KataFF/tbt-pcie-adapter/connectors.kicad_sch

## KiCad design connectors.kicad_sch (2025-07-04)

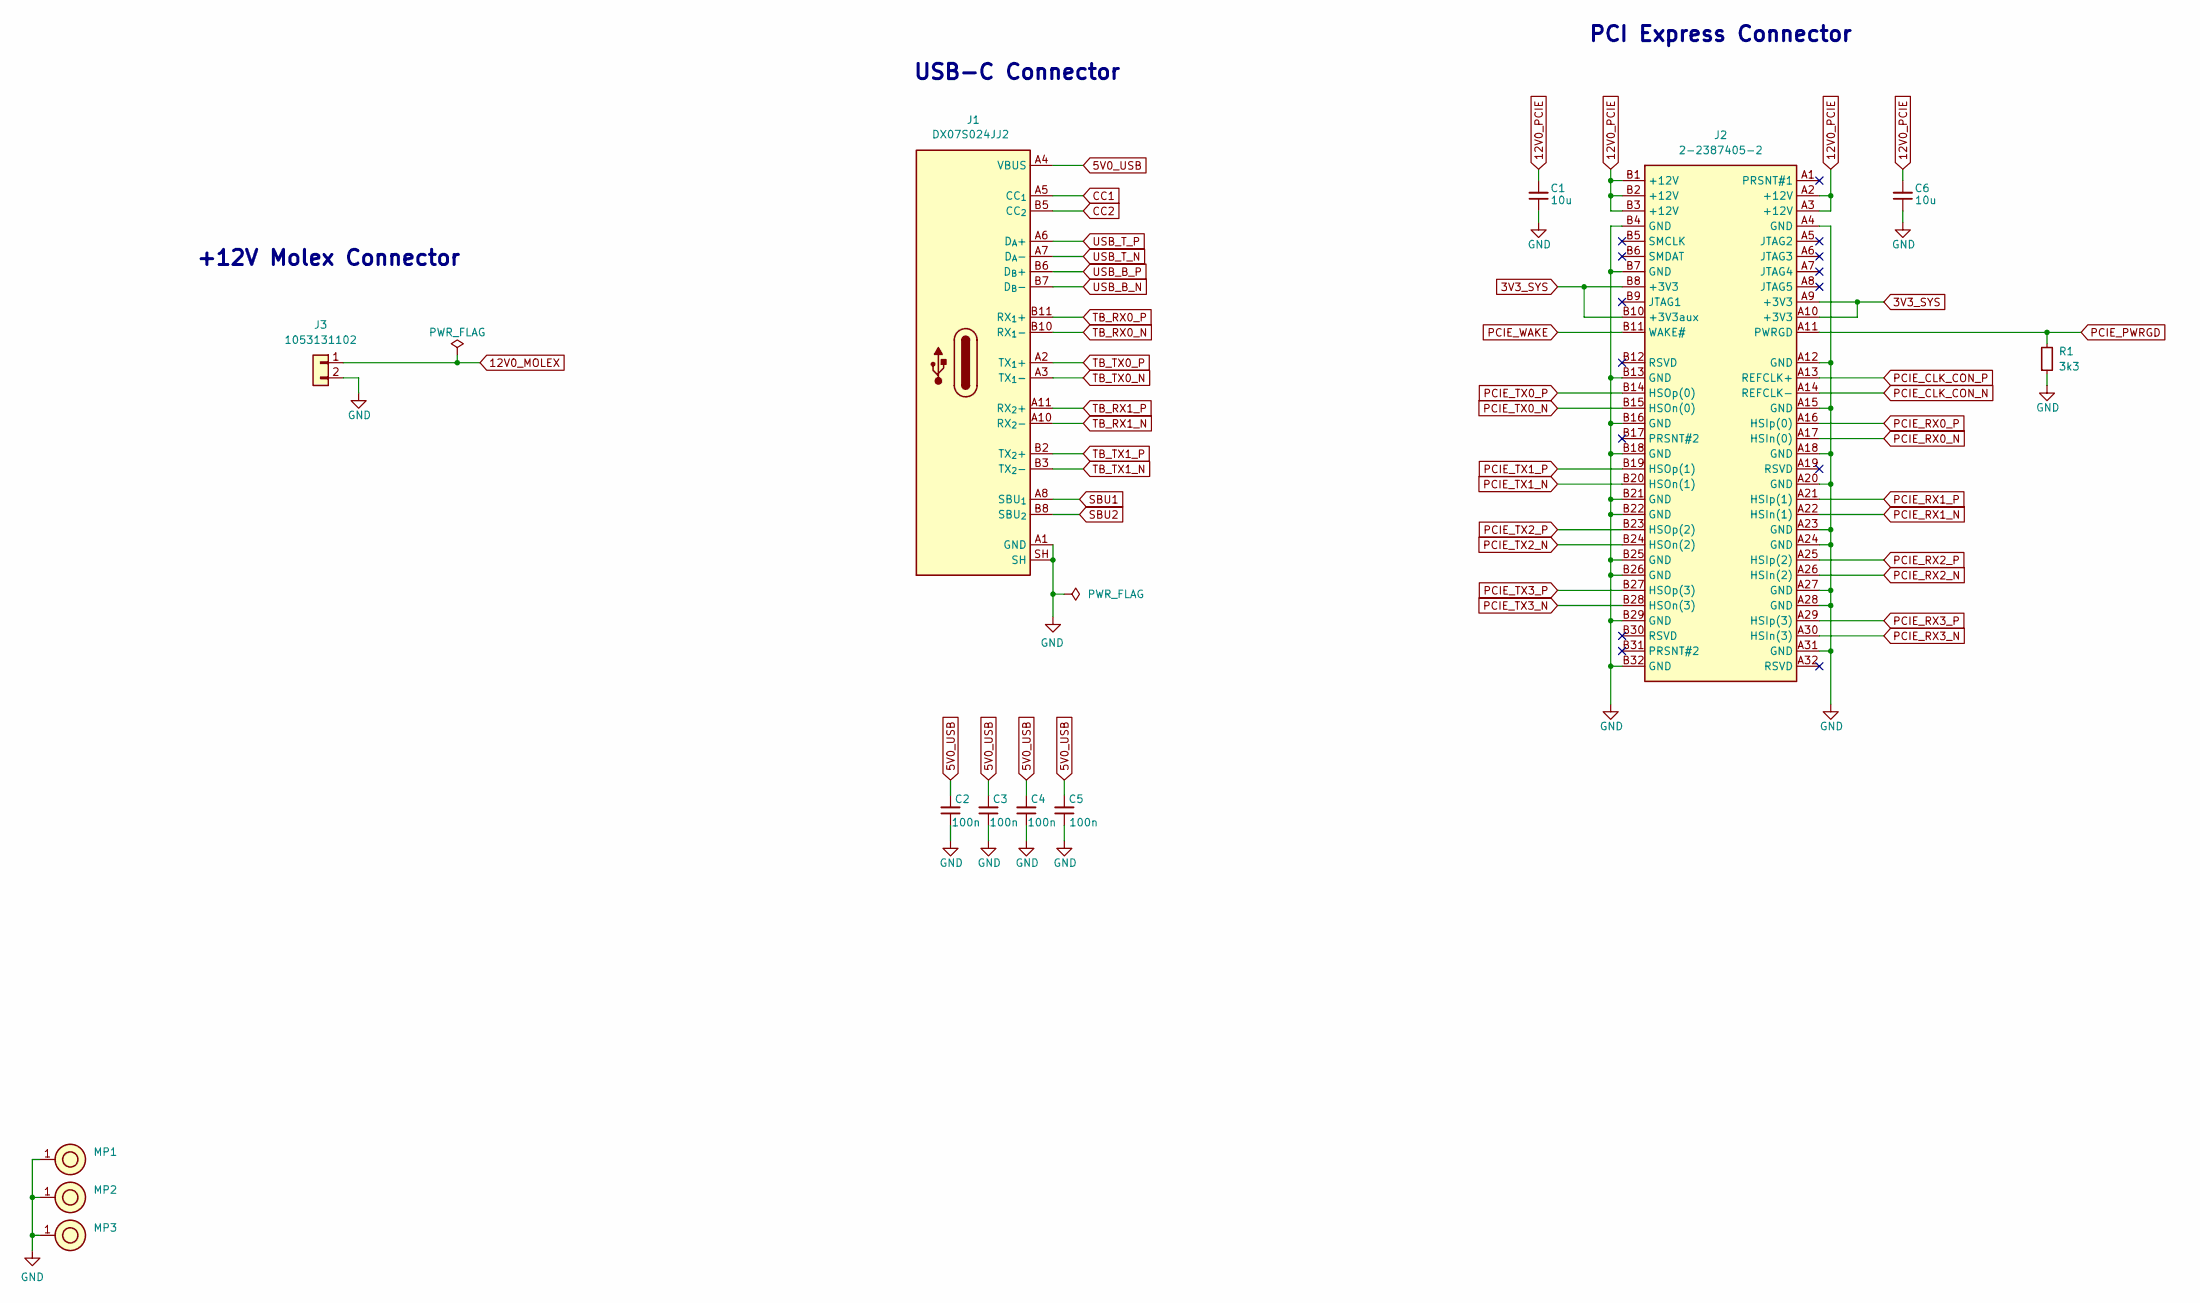
[picture p2: schematic connectors.kicad_sch]

Parts:
C1, C6: C_10u_0805_35V; C_0805_2012Metric; Voltage 35V; MPN GRM21BR6YA106KE43L
C2, C3, C4, C5: C_100n_0402; C_0402_1005Metric; Voltage 50V; MPN GRM155R61H104KE14D
J1: USB-C_JAE_DX07S024JJ2; USB-C_Receptacle_JAE_DX07S024JJ2; MPN DX07S024JJ2
J2: PCIe_x4_Conn_EdgeMount_Open; PCIE_TE_2-2387405-2; MPN 2-2387405-2
J3: Molex_Nano-Fit_1x2_1053131102; Conn_Molex_Nano-Fit_1x2_1053131102; MPN 1053131102
MP1, MP2, MP3: MP_Pad6mm_Drill3mm
R1: R_3k3_0402; R_0402_1005Metric; Tolerance 1%; MPN CR0402-FX-3301GLF

Connections:
3V3_SYS: J2.A9 (+3V3), J2.A10 (+3V3), J2.B8 (+3V3), J2.B10 (+3V3aux)
5V0_USB: C2.2, C3.2, C4.2, C5.2, J1.A4 (VBUS), J1.A9 (VBUS), J1.B4 (VBUS), J1.B9 (VBUS)
12V0_MOLEX: J3.1
12V0_PCIE: C1.2, C6.2, J2.A2 (+12V), J2.A3 (+12V), J2.B1 (+12V), J2.B2 (+12V), J2.B3 (+12V)
CC1: J1.A5 (CC_{1})
CC2: J1.B5 (CC_{2})
GND: C1.1, C2.1, C3.1, C4.1, C5.1, C6.1, J1.A1 (GND), J1.A12 (GND), J1.B1 (GND), J1.B12 (GND), J1.SH, J2.A4 (GND), J2.A12 (GND), J2.A15 (GND), J2.A18 (GND), J2.A20 (GND), J2.A23 (GND), J2.A24 (GND), J2.A27 (GND), J2.A28 (GND), J2.A31 (GND), J2.B4 (GND), J2.B7 (GND), J2.B13 (GND), J2.B16 (GND), J2.B18 (GND), J2.B21 (GND), J2.B22 (GND), J2.B25 (GND), J2.B26 (GND), J2.B29 (GND), J2.B32 (GND), J3.2, MP1.1, MP2.1, MP3.1, R1.1
PCIE_CLK_CON_N: J2.A14 (REFCLK-)
PCIE_CLK_CON_P: J2.A13 (REFCLK+)
PCIE_PWRGD: J2.A11 (PWRGD), R1.2
PCIE_RX0_N: J2.A17 (HSIn(0))
PCIE_RX0_P: J2.A16 (HSIp(0))
PCIE_RX1_N: J2.A22 (HSIn(1))
PCIE_RX1_P: J2.A21 (HSIp(1))
PCIE_RX2_N: J2.A26 (HSIn(2))
PCIE_RX2_P: J2.A25 (HSIp(2))
PCIE_RX3_N: J2.A30 (HSIn(3))
PCIE_RX3_P: J2.A29 (HSIp(3))
PCIE_TX0_N: J2.B15 (HSOn(0))
PCIE_TX0_P: J2.B14 (HSOp(0))
PCIE_TX1_N: J2.B20 (HSOn(1))
PCIE_TX1_P: J2.B19 (HSOp(1))
PCIE_TX2_N: J2.B24 (HSOn(2))
PCIE_TX2_P: J2.B23 (HSOp(2))
PCIE_TX3_N: J2.B28 (HSOn(3))
PCIE_TX3_P: J2.B27 (HSOp(3))
PCIE_WAKE: J2.B11 (WAKE#)
SBU1: J1.A8 (SBU_{1})
SBU2: J1.B8 (SBU_{2})
TB_RX0_N: J1.B10 (RX_{1}-)
TB_RX0_P: J1.B11 (RX_{1}+)
TB_RX1_N: J1.A10 (RX_{2}-)
TB_RX1_P: J1.A11 (RX_{2}+)
TB_TX0_N: J1.A3 (TX_{1}-)
TB_TX0_P: J1.A2 (TX_{1}+)
TB_TX1_N: J1.B3 (TX_{2}-)
TB_TX1_P: J1.B2 (TX_{2}+)
USB_B_N: J1.B7 (D_{B}-)
USB_B_P: J1.B6 (D_{B}+)
USB_T_N: J1.A7 (D_{A}-)
USB_T_P: J1.A6 (D_{A}+)

Notes on the sheet:
+12V Molex Connector
PCI Express Connector
USB-C Connector
