KataFF/tbt-pcie-adapter/power.kicad_sch

## KiCad design power.kicad_sch (2025-07-04)

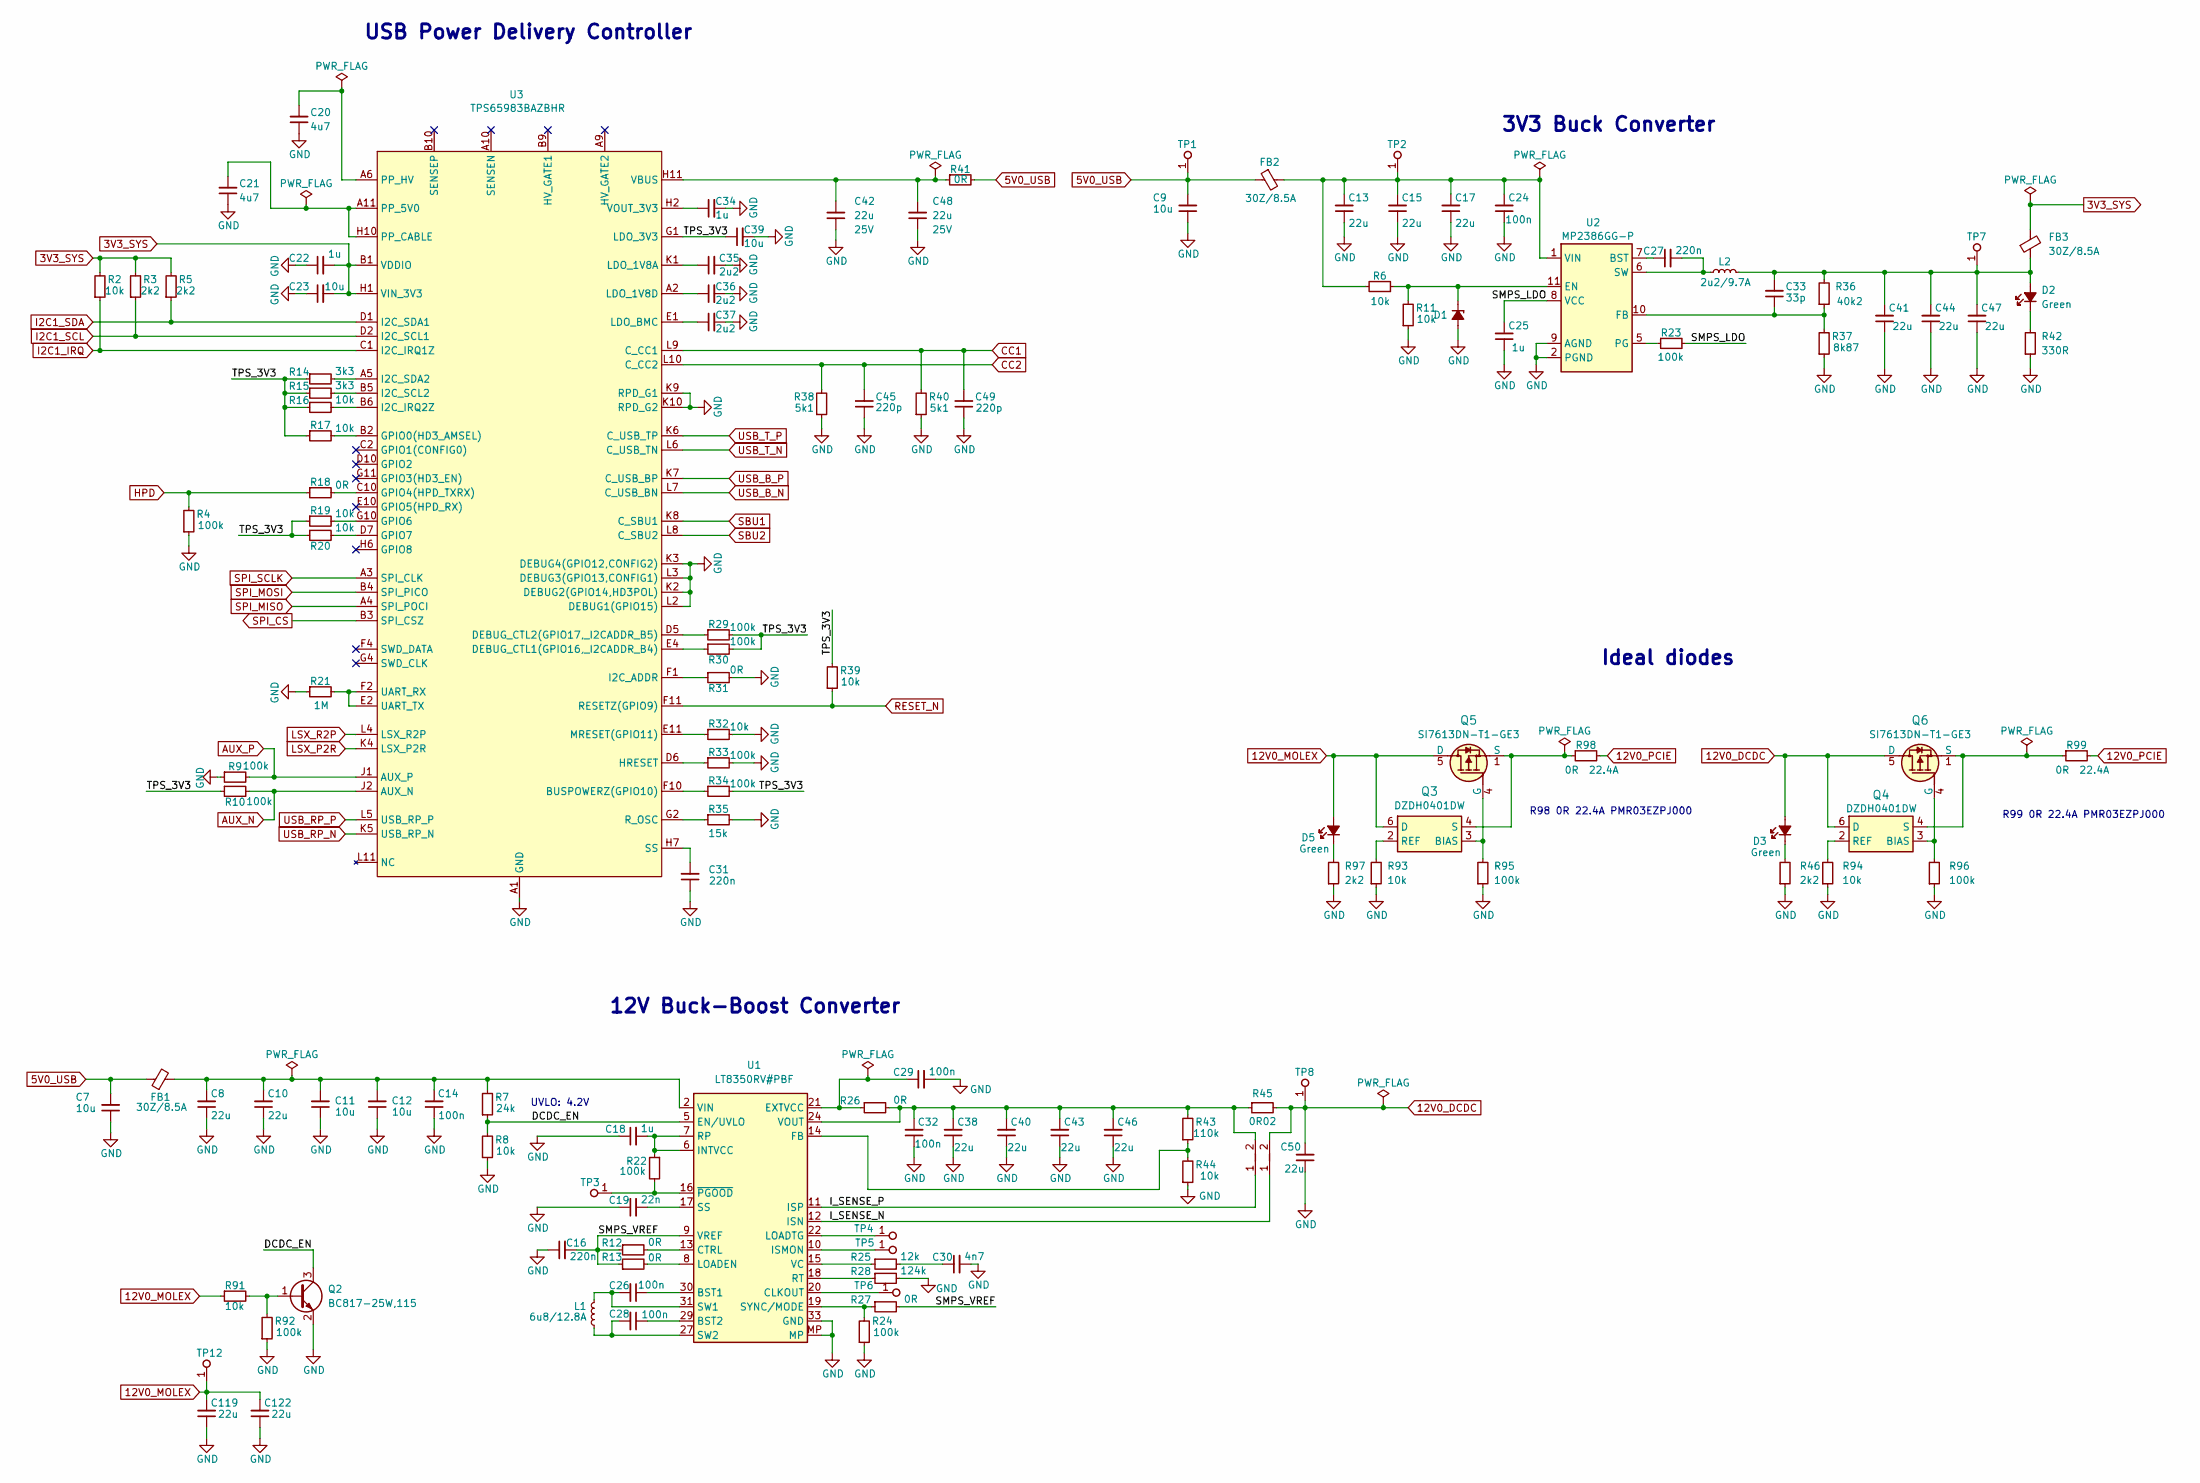
[picture p3: schematic power.kicad_sch]

Parts:
C7, C9, C11, C12: C_10u_0805_35V; C_0805_2012Metric; Voltage 35V; MPN GRM21BR6YA106KE43L
C8, C10, C13, C15, C17: C_22u_1206_35V; C_1206_3216Metric; Voltage 35V; MPN 3216X5R1V226M160AC
C14, C24, C26, C28, C29, C32: C_100n_0402; C_0402_1005Metric; Voltage 50V; MPN GRM155R61H104KE14D
C16, C27, C31: C_220n_0402; C_0402_1005Metric; MPN CC0402KRX5R6BB224
C18, C22, C25, C34: C_1u_0402; C_0402_1005Metric; MPN C1005X6S1A105K050BC
C19: C_22n_0402; C_0402_1005Metric; MPN GCM155R71H223MA55D
C20, C21: C_4u7_25V_0402; C_0402_1005Metric; Voltage 25V; MPN GRM155C61E475ME15J
C23, C39: C_10u_0402; C_0402_1005Metric; MPN CC0402MRX5R5BB106
C30: C_4n7_0402; C_0402_1005Metric; MPN CGA2B3X7S2A472K050BB
C33: C_33p_0402; C_0402_1005Metric; MPN 04025A330FAT2A
C35, C36, C37: C_2u2_0402; C_0402_1005Metric; MPN C1005X5R1A225K050BC
C38, C40, C43, C46, C50, C119, C122: C_22u_16V_0603; C_0603_1608Metric; Voltage 16V; MPN CL10A226MO7JZNC
C41, C44, C47: C_22u_0603; C_0603_1608Metric; MPN GRM188R60J226MEA0D
C42, C48: C_22u_25V_0805; C_0805_2012Metric; Voltage 25V; MPN CL21A226MAYNNNE
C45, C49: C_220p_0402; C_0402_1005Metric; MPN 04025C221JAT2A
D1: MM3Z3V3C; D_SOD-323F; MPN MM3Z3V3C
D2, D3, D5: LED_G_0603_KP-1608CGCK; LED_0603_1608Metric_G; MPN KP-1608CGCK
FB1, FB2, FB3: FB_30Z_8.5A_Murata-BLM21SN_0805; FB_0805_2012Metric; MPN BLM21SN300SZ1D
L1: L_6u8_12.8A_Coilcraft-XAL7070; L_Coilcraft-XAL7070; MPN XAL7070-682MEC
L2: L_2u2_9.7A_Coilcraft-XAL5030; L_Coilcraft-XAL5030; MPN XAL5030-222MEC
Q2: BC817-25W; SOT-323; MPN BC817-25W,115
Q3, Q4: DZDH0401DW; SOT-363; MPN DZDH0401DW
Q5, Q6: SI7613DN-T1-GE3; Vishay_PowerPAK_1212-8_Single; MPN SI7613DN-T1-GE3
R2, R6, R8, R11, R16, R17, R19, R20, R32, R39, R44, R91, R93, R94: R_10k_0402; R_0402_1005Metric; Tolerance 1%; MPN CR0402-FX-1002GLF
R3, R5, R46, R97: R_2k2_0402; R_0402_1005Metric; Tolerance 1%; MPN CR0402-FX-2201GLF
R4, R9, R10, R22, R23, R24, R29, R30, R33, R34, R92, R95, R96: R_100k_0402; R_0402_1005Metric; Tolerance 1%; MPN CR0402-FX-1003GLF
R7: R_24k_0402; R_0402_1005Metric; Tolerance 1%; MPN CR0402-FX-2402GLF
R12, R13, R18, R26, R27, R31: R_0R_0402; R_0402_1005Metric; MPN ERJ2GE0R00X
R14, R15: R_3k3_0402; R_0402_1005Metric; Tolerance 1%; MPN CR0402-FX-3301GLF
R21: R_1M_0402; R_0402_1005Metric; Tolerance 1%; MPN CR0402-FX-1004GLF
R25: R_12k_0402; R_0402_1005Metric; Tolerance 1%; MPN CR0402-FX-1202GLF
R28: R_124k_0402; R_0402_1005Metric; Tolerance 1%; MPN CR0402-FX-1243GLF
R35: R_15k_0.1%_0402; R_0402_1005Metric; Tolerance 0.1%; MPN ERA-2ARB153X
R36: R_40k2_0402; R_0402_1005Metric; Tolerance 1%; MPN CR0402-FX-4022GLF
R37: R_8k87_0402; R_0402_1005Metric; Tolerance 1%; MPN CR0402-FX-8871GLF
R38, R40: R_5k1_0402; R_0402_1005Metric; Tolerance 1%; MPN CR0402-FX-5101GLF
R41: R_0R_0603; R_0603_1608Metric; MPN CR0603-J/-000ELF
R42: R_330R_0402; R_0402_1005Metric; Tolerance 1%; MPN CR0402-FX-3300GLF
R43: R_110k_0402; R_0402_1005Metric; Tolerance 1%; MPN CR0402-FX-1103GLF
R45: R_0R02_1206; R_1206_3216Metric; Tolerance 1%; MPN WSLP1206R0200FEA
R98, R99: R_0R_22.4A_0603; R_0603_1608Metric; Tolerance template_tolerance; MPN PMR03EZPJ000
TP1, TP2, TP3, TP5, TP7, TP8, TP12: TP_1mm_SMD; TP_SMD_1mm
TP4, TP6: TP_0.75mm_SMD; TP_SMD_0.75mm
TP10, TP11: Net-Tie_P0.1mm; NetTie-2_SMD_Pad0.1mm
U1: LT8350RV; QFN-32-4EP_4x6mm_P0.5mm; MPN LT8350RV#PBF
U2: MP2386GG; QFN-11_2x2mm_P0.5mm; MPN MP2386GG-P
U3: TPS65983BAZBHR; IC_TPS65983BAZBHR; MPN TPS65983BAZBHR

Connections:
3V3_SYS: C22.2, C23.2, FB3.2, R2.2, R3.2, R5.2, U3.B1 (VDDIO), U3.H1 (VIN_3V3)
5V0_USB: C7.2, C9.2, FB1.1, FB2.1, R41.2, TP1.1
12V0_DCDC: C50.2, D3.2 (A), Q4.6 (D), Q6.5 (D), R45.2, TP8.1, TP11.2
12V0_MOLEX: C119.2, C122.2, D5.2 (A), Q3.6 (D), Q5.5 (D), R91.1, TP12.1
12V0_PCIE: R98.2, R99.2
AUX_N: R10.2, U3.J2 (AUX_N)
AUX_P: R9.2, U3.J1 (AUX_P)
CC1: C49.2, R40.2, U3.L9 (C_CC1)
CC2: C45.2, R38.2, U3.L10 (C_CC2)
DCDC_EN: Q2.3 (C), R7.1, R8.2, U1.5 (EN/UVLO)
GND: C7.1, C8.1, C9.1, C10.1, C11.1, C12.1, C13.1, C14.1, C15.1, C16.1, C17.1, C18.1, C19.1, C20.1, C21.1, C22.1, C23.1, C24.1, C25.1, C29.2, C30.2, C31.1, C32.1, C34.2, C35.2, C36.2, C37.2, C38.1, C39.2, C40.1, C41.1, C42.1, C43.1, C44.1, C45.1, C46.1, C47.1, C48.1, C49.1, C50.1, C119.1, C122.1, D1.2 (A), Q2.2 (E), R4.1, R8.1, R9.1, R11.1, R21.1, R24.1, R28.2, R31.2, R32.2, R33.2, R35.2, R37.1, R38.1, R40.1, R42.1, R44.1, R46.1, R92.1, R93.1, R94.1, R95.1, R96.1, R97.1, U1.33 (GND), U1.34 (GND), U1.35 (GND), U1.36 (GND), U1.MP, U2.2 (PGND), U2.3 (PGND), U2.4 (PGND), U2.9 (AGND), U3.A1 (GND), U3.B8 (GND), U3.D8 (GND), U3.E5 (GND), U3.E6 (GND), U3.E7 (GND), U3.E8 (GND), U3.F5 (GND), U3.F6 (GND), U3.F7 (GND), U3.F8 (GND), U3.G5 (GND), U3.G6 (GND), U3.G7 (GND), U3.G8 (GND), U3.H4 (GND), U3.H5 (GND), U3.H8 (GND), U3.K2 (DEBUG2(GPIO14,HD3POL)), U3.K3 (DEBUG4(GPIO12,CONFIG2)), U3.K9 (RPD_G1), U3.K10 (RPD_G2), U3.L1 (GND), U3.L2 (DEBUG1(GPIO15)), U3.L3 (DEBUG3(GPIO13,CONFIG1))
HPD: R4.2, R18.1
I2C1_IRQ: R2.1, U3.C1 (I2C_IRQ1Z)
I2C1_SCL: R3.1, U3.D2 (I2C_SCL1)
I2C1_SDA: R5.1, U3.D1 (I2C_SDA1)
I_SENSE_N: TP11.1, U1.12 (ISN)
I_SENSE_P: TP10.1, U1.11 (ISP)
LSX_P2R: U3.K4 (LSX_P2R)
LSX_R2P: U3.L4 (LSX_R2P)
unnamed: C8.2, C10.2, C11.2, C12.2, C14.2, FB1.2, R7.2, U1.2 (VIN), U1.3 (VIN)
unnamed: C13.2, C15.2, C17.2, C24.2, FB2.2, R6.2, TP2.1, U2.1 (VIN)
unnamed: C18.2, R22.1, U1.6 (INTVCC), U1.7 (RP)
unnamed: C19.2, U1.17 (SS)
unnamed: C20.2, U3.A6 (PP_HV), U3.A7 (PP_HV), U3.A8 (PP_HV), U3.B7 (PP_HV)
unnamed: C21.2, U3.A11 (PP_5V0), U3.B11 (PP_5V0), U3.C11 (PP_5V0), U3.D11 (PP_5V0), U3.H10 (PP_CABLE)
unnamed: C26.1, U1.30 (BST1)
unnamed: C26.2, L1.1, U1.31 (SW1), U1.32 (SW1)
unnamed: C27.1, U2.7 (BST)
unnamed: C27.2, L2.1, U2.6 (SW)
unnamed: C28.1, U1.29 (BST2)
unnamed: C28.2, L1.2, U1.27 (SW2), U1.28 (SW2)
unnamed: C29.1, R26.1, U1.21 (EXTVCC)
unnamed: C30.1, R25.2
unnamed: C31.2, U3.H7 (SS)
unnamed: C32.2, C38.2, C40.2, C43.2, C46.2, R26.2, R43.2, R45.1, TP10.2, U1.24 (VOUT), U1.25 (VOUT)
unnamed: C33.1, R36.1, R37.2, U2.10 (FB)
unnamed: C33.2, C41.2, C44.2, C47.2, D2.2 (A), FB3.1, L2.2, R36.2, TP7.1
unnamed: C34.1, U3.H2 (VOUT_3V3)
unnamed: C35.1, U3.K1 (LDO_1V8A)
unnamed: C36.1, U3.A2 (LDO_1V8D)
unnamed: C37.1, U3.E1 (LDO_BMC)
unnamed: C42.2, C48.2, R41.1, U3.H11 (VBUS), U3.J10 (VBUS), U3.J11 (VBUS), U3.K11 (VBUS)
unnamed: D1.1 (C), R6.1, R11.2, U2.11 (EN)
unnamed: D2.1 (C), R42.2
unnamed: D3.1 (C), R46.2
unnamed: D5.1 (C), R97.2
unnamed: Q2.1 (B), R91.2, R92.2
unnamed: Q3.2 (REF), R93.2
unnamed: Q3.3 (BIAS), Q5.4 (G), R95.2
unnamed: Q3.4 (S), Q5.1 (S), Q5.2 (S), Q5.3 (S), R98.1
unnamed: Q4.2 (REF), R94.2
unnamed: Q4.3 (BIAS), Q6.4 (G), R96.2
unnamed: Q4.4 (S), Q6.1 (S), Q6.2 (S), Q6.3 (S), R99.1
unnamed: R12.2, U1.13 (CTRL)
unnamed: R13.2, U1.8 (LOADEN)
unnamed: R14.2, U3.A5 (I2C_SDA2)
unnamed: R15.2, U3.B5 (I2C_SCL2)
unnamed: R16.2, U3.B6 (I2C_IRQ2Z)
unnamed: R17.2, U3.B2 (GPIO0(HD3_AMSEL))
unnamed: R18.2, U3.C10 (GPIO4(HPD_TXRX))
unnamed: R19.2, U3.G10 (GPIO6)
unnamed: R20.2, U3.D7 (GPIO7)
unnamed: R21.2, U3.E2 (UART_TX), U3.F2 (UART_RX)
unnamed: R22.2, TP3.1, U1.16 (~PGOOD)
unnamed: R23.1, U2.5 (PG)
unnamed: R24.2, R27.1, U1.19 (SYNC/MODE)
unnamed: R25.1, U1.15 (VC)
unnamed: R28.1, U1.18 (RT)
unnamed: R29.1, U3.D5 (DEBUG_CTL2(GPIO17,_I2CADDR_B5))
unnamed: R30.1, U3.E4 (DEBUG_CTL1(GPIO16,_I2CADDR_B4))
unnamed: R31.1, U3.F1 (I2C_ADDR)
unnamed: R32.1, U3.E11 (MRESET(GPIO11))
unnamed: R33.1, U3.D6 (HRESET)
unnamed: R34.1, U3.F10 (BUSPOWERZ(GPIO10))
unnamed: R35.1, U3.G2 (R_OSC)
unnamed: R43.1, R44.2, U1.14 (FB)
unnamed: TP4.1, U1.22 (LOADTG)
unnamed: TP5.1, U1.10 (ISMON)
unnamed: TP6.1, U1.20 (CLKOUT)
RESET_N: R39.1, U3.F11 (RESETZ(GPIO9))
SBU1: U3.K8 (C_SBU1)
SBU2: U3.L8 (C_SBU2)
SMPS_LDO: C25.2, R23.2, U2.8 (VCC)
SMPS_VREF: C16.2, R12.1, R13.1, R27.2, U1.9 (VREF)
SPI_CS: U3.B3 (SPI_CSZ)
SPI_MISO: U3.A4 (SPI_POCI)
SPI_MOSI: U3.B4 (SPI_PICO)
SPI_SCLK: U3.A3 (SPI_CLK)
TPS_3V3: C39.1, R10.1, R14.1, R15.1, R16.1, R17.1, R19.1, R20.1, R29.2, R30.2, R34.2, R39.2, U3.G1 (LDO_3V3)
USB_B_N: U3.L7 (C_USB_BN)
USB_B_P: U3.K7 (C_USB_BP)
USB_RP_N: U3.K5 (USB_RP_N)
USB_RP_P: U3.L5 (USB_RP_P)
USB_T_N: U3.L6 (C_USB_TN)
USB_T_P: U3.K6 (C_USB_TP)

Notes on the sheet:
UVLO: 4.2V
R99 0R 22.4A PMR03EZPJ000
Ideal diodes
USB Power Delivery Controller
12V Buck-Boost Converter
3V3 Buck Converter
R98 0R 22.4A PMR03EZPJ000
