KataFF/tbt-pcie-adapter/tb-power.kicad_sch

## KiCad design tb-power.kicad_sch (2025-07-04)

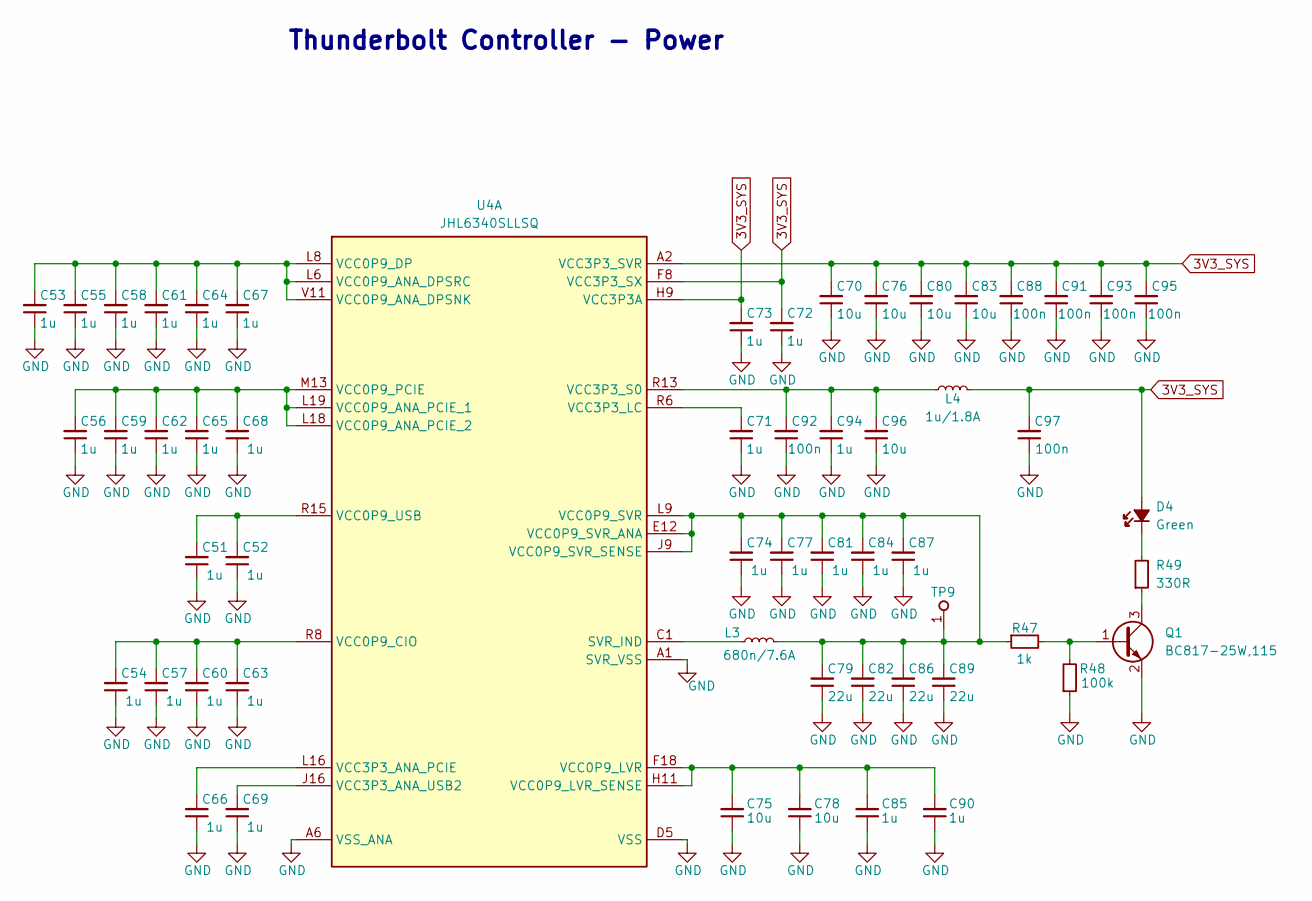
[picture p4: schematic tb-power.kicad_sch]

Parts:
C51, C52, C53, C54, C55, C56, C57, C58, C59, C60, C61, C62, C63, C64, C65, C66, C67, C68, C69, C71, C72, C73, C74, C77, C81, C84, C85, C87, C90, C94: C_1u_0402; C_0402_1005Metric; MPN C1005X6S1A105K050BC
C70, C75, C76, C78, C80, C83, C96: C_10u_0402; C_0402_1005Metric; MPN CC0402MRX5R5BB106
C79, C82, C86, C89: C_22u_0603; C_0603_1608Metric; MPN GRM188R60J226MEA0D
C88, C91, C92, C93, C95, C97: C_100n_0402; C_0402_1005Metric; Voltage 50V; MPN GRM155R61H104KE14D
D4: LED_G_0603_KP-1608CGCK; LED_0603_1608Metric_G; MPN KP-1608CGCK
L3: L_680n_7.6A_IHLP1616BZ; L_Vishay-IHLP1616BZ; MPN IHLP1616BZERR68M5A
L4: L_1u_1.8A_0603; L_0603_1608Metric; MPN DFE18SBN1R0ME0L
Q1: BC817-25W; SOT-323; MPN BC817-25W,115
R47: R_1k_0402; R_0402_1005Metric; Tolerance 1%; MPN CR0402-FX-1001GLF
R48: R_100k_0402; R_0402_1005Metric; Tolerance 1%; MPN CR0402-FX-1003GLF
R49: R_330R_0402; R_0402_1005Metric; Tolerance 1%; MPN CR0402-FX-3300GLF
TP9: TP_1mm_SMD; TP_SMD_1mm
U4: JHL6340SLLSQ; MPN JHL6340SLLSQ

Connections:
3V3_SYS: C70.2, C72.2, C73.2, C76.2, C80.2, C83.2, C88.2, C91.2, C93.2, C95.2, C97.2, D4.2 (A), L4.2, U4.A2 (VCC3P3_SVR), U4.A3 (VCC3P3_SVR), U4.B3 (VCC3P3_SVR), U4.F8 (VCC3P3_SX), U4.H9 (VCC3P3A)
GND: C51.1, C52.1, C53.1, C54.1, C55.1, C56.1, C57.1, C58.1, C59.1, C60.1, C61.1, C62.1, C63.1, C64.1, C65.1, C66.1, C67.1, C68.1, C69.1, C70.1, C71.1, C72.1, C73.1, C74.1, C75.1, C76.1, C77.1, C78.1, C79.1, C80.1, C81.1, C82.1, C83.1, C84.1, C85.1, C86.1, C87.1, C88.1, C89.1, C90.1, C91.1, C92.1, C93.1, C94.1, C95.1, C96.1, C97.1, Q1.2 (E), R48.1, U4.A1 (SVR_VSS), U4.A6 (VSS_ANA), U4.A8 (VSS_ANA), U4.A10 (VSS_ANA), U4.A12 (VSS_ANA), U4.A14 (VSS_ANA), U4.A16 (VSS_ANA), U4.A18 (VSS_ANA), U4.A20 (VSS_ANA), U4.A22 (VSS_ANA), U4.AA22 (VSS_ANA), U4.AA23 (VSS_ANA), U4.AB1 (VSS), U4.AB6 (VSS_ANA), U4.AB8 (VSS_ANA), U4.AB10 (VSS_ANA), U4.AB12 (VSS_ANA), U4.AB14 (VSS_ANA), U4.AB16 (VSS_ANA), U4.AB18 (VSS_ANA), U4.AB20 (VSS_ANA), U4.AB22 (VSS_ANA), U4.AC2 (VSS), U4.AC6 (VSS_ANA), U4.AC8 (VSS_ANA), U4.AC10 (VSS_ANA), U4.AC12 (VSS_ANA), U4.AC14 (VSS_ANA), U4.AC16 (VSS_ANA), U4.AC18 (VSS_ANA), U4.AC20 (VSS_ANA), U4.AC22 (VSS_ANA), U4.B1 (SVR_VSS), U4.B2 (SVR_VSS), U4.B6 (VSS_ANA), U4.B8 (VSS_ANA), U4.B10 (VSS_ANA), U4.B12 (VSS_ANA), U4.B14 (VSS_ANA), U4.B16 (VSS_ANA), U4.B18 (VSS_ANA), U4.B20 (VSS_ANA), U4.B22 (VSS_ANA), U4.D5 (VSS), U4.D8 (VSS_ANA), U4.D9 (VSS_ANA), U4.D11 (VSS_ANA), U4.D12 (VSS_ANA), U4.D13 (VSS_ANA), U4.D15 (VSS_ANA), U4.D16 (VSS_ANA), U4.D18 (VSS_ANA), U4.E4 (VSS), U4.E5 (VSS), U4.E6 (VSS), U4.E8 (VSS_ANA), U4.E9 (VSS_ANA), U4.E11 (VSS_ANA), U4.E15 (VSS_ANA), U4.E16 (VSS_ANA), U4.E22 (VSS_ANA), U4.E23 (VSS_ANA), U4.F5 (VSS), U4.F6 (VSS), U4.F9 (VSS_ANA), U4.F16 (VSS_ANA), U4.F20 (VSS_ANA), U4.G22 (VSS_ANA), U4.G23 (VSS_ANA), U4.H1 (VSS_ANA), U4.H2 (VSS_ANA), U4.H5 (VSS), U4.H8 (VSS), U4.H12 (VSS_ANA), U4.H13 (VSS_ANA), U4.H15 (VSS_ANA), U4.H16 (VSS_ANA), U4.H20 (VSS_ANA), U4.J5 (VSS_ANA), U4.J8 (VSS), U4.J12 (VSS), U4.J13 (VSS), U4.J15 (VSS), U4.J18 (VSS_ANA), U4.J19 (VSS_ANA), U4.J20 (VSS_ANA), U4.J22 (VSS_ANA), U4.J23 (VSS_ANA), U4.K1 (VSS_ANA), U4.K2 (VSS_ANA), U4.L5 (VSS_ANA), U4.L13 (VSS), U4.L20 (VSS_ANA), U4.L22 (VSS_ANA), U4.L23 (VSS_ANA), U4.M1 (VSS_ANA), U4.M2 (VSS_ANA), U4.M5 (VSS_ANA), U4.M11 (VSS), U4.M12 (VSS), U4.M19 (VSS_ANA), U4.M20 (VSS_ANA), U4.N5 (VSS_ANA), U4.N8 (VSS), U4.N9 (VSS), U4.N11 (VSS), U4.N12 (VSS), U4.N13 (VSS), U4.N20 (VSS_ANA), U4.N22 (VSS_ANA), U4.N23 (VSS_ANA), U4.P1 (VSS_ANA), U4.P2 (VSS_ANA), U4.R5 (VSS_ANA), U4.R18 (VSS_ANA), U4.R19 (VSS_ANA), U4.R20 (VSS_ANA), U4.R22 (VSS_ANA), U4.R23 (VSS_ANA), U4.T1 (VSS_ANA), U4.T2 (VSS_ANA), U4.T5 (VSS_ANA), U4.T6 (VSS), U4.T8 (VSS), U4.T9 (VSS), U4.T13 (VSS), U4.T15 (VSS), U4.T16 (VSS), U4.T18 (VSS), U4.T20 (VSS_ANA), U4.U22 (VSS_ANA), U4.U23 (VSS_ANA), U4.V5 (VSS_ANA), U4.V6 (VSS_ANA), U4.V8 (VSS_ANA), U4.V9 (VSS_ANA), U4.V15 (VSS_ANA), U4.V16 (VSS_ANA), U4.V20 (VSS_ANA), U4.W5 (VSS_ANA), U4.W6 (VSS_ANA), U4.W8 (VSS_ANA), U4.W9 (VSS_ANA), U4.W20 (VSS_ANA), U4.W22 (VSS_ANA), U4.W23 (VSS_ANA), U4.Y9 (VSS_ANA), U4.Y13 (VSS_ANA), U4.Y20 (VSS_ANA)
unnamed: C51.2, C52.2, U4.R15 (VCC0P9_USB), U4.R16 (VCC0P9_USB)
unnamed: C53.2, C55.2, C58.2, C61.2, C64.2, C67.2, U4.L6 (VCC0P9_ANA_DPSRC), U4.L8 (VCC0P9_DP), U4.L11 (VCC0P9_DP), U4.L12 (VCC0P9_DP), U4.M6 (VCC0P9_ANA_DPSRC), U4.M8 (VCC0P9_DP), U4.T11 (VCC0P9_DP), U4.T12 (VCC0P9_DP), U4.V11 (VCC0P9_ANA_DPSNK), U4.V12 (VCC0P9_ANA_DPSNK), U4.V13 (VCC0P9_ANA_DPSNK)
unnamed: C54.2, C57.2, C60.2, C63.2, U4.R8 (VCC0P9_CIO), U4.R9 (VCC0P9_CIO), U4.R11 (VCC0P9_CIO), U4.R12 (VCC0P9_CIO)
unnamed: C56.2, C59.2, C62.2, C65.2, C68.2, U4.L18 (VCC0P9_ANA_PCIE_2), U4.L19 (VCC0P9_ANA_PCIE_1), U4.M13 (VCC0P9_PCIE), U4.M15 (VCC0P9_PCIE), U4.M16 (VCC0P9_PCIE), U4.M18 (VCC0P9_ANA_PCIE_2), U4.N18 (VCC0P9_ANA_PCIE_2), U4.N19 (VCC0P9_ANA_PCIE_1)
unnamed: C66.2, U4.L16 (VCC3P3_ANA_PCIE)
unnamed: C69.2, U4.J16 (VCC3P3_ANA_USB2)
unnamed: C71.2, U4.R6 (VCC3P3_LC)
unnamed: C74.2, C77.2, C79.2, C81.2, C82.2, C84.2, C86.2, C87.2, C89.2, L3.2, R47.1, TP9.1, U4.E12 (VCC0P9_SVR_ANA), U4.E13 (VCC0P9_SVR_ANA), U4.F11 (VCC0P9_SVR_ANA), U4.F12 (VCC0P9_SVR_ANA), U4.F13 (VCC0P9_SVR_ANA), U4.F15 (VCC0P9_SVR_ANA), U4.J9 (VCC0P9_SVR_SENSE), U4.L9 (VCC0P9_SVR), U4.M9 (VCC0P9_SVR)
unnamed: C75.2, C78.2, C85.2, C90.2, U4.F18 (VCC0P9_LVR), U4.H11 (VCC0P9_LVR_SENSE), U4.H18 (VCC0P9_LVR), U4.J11 (VCC0P9_LVR)
unnamed: C92.2, C94.2, C96.2, L4.1, U4.R13 (VCC3P3_S0)
unnamed: D4.1 (C), R49.2
unnamed: L3.1, U4.C1 (SVR_IND), U4.C2 (SVR_IND), U4.D1 (SVR_IND)
unnamed: Q1.1 (B), R47.2, R48.2
unnamed: Q1.3 (C), R49.1

Notes on the sheet:
Thunderbolt Controller - Power
