KataFF/tbt-pcie-adapter/tb.kicad_sch

## KiCad design tb.kicad_sch (2025-07-04)

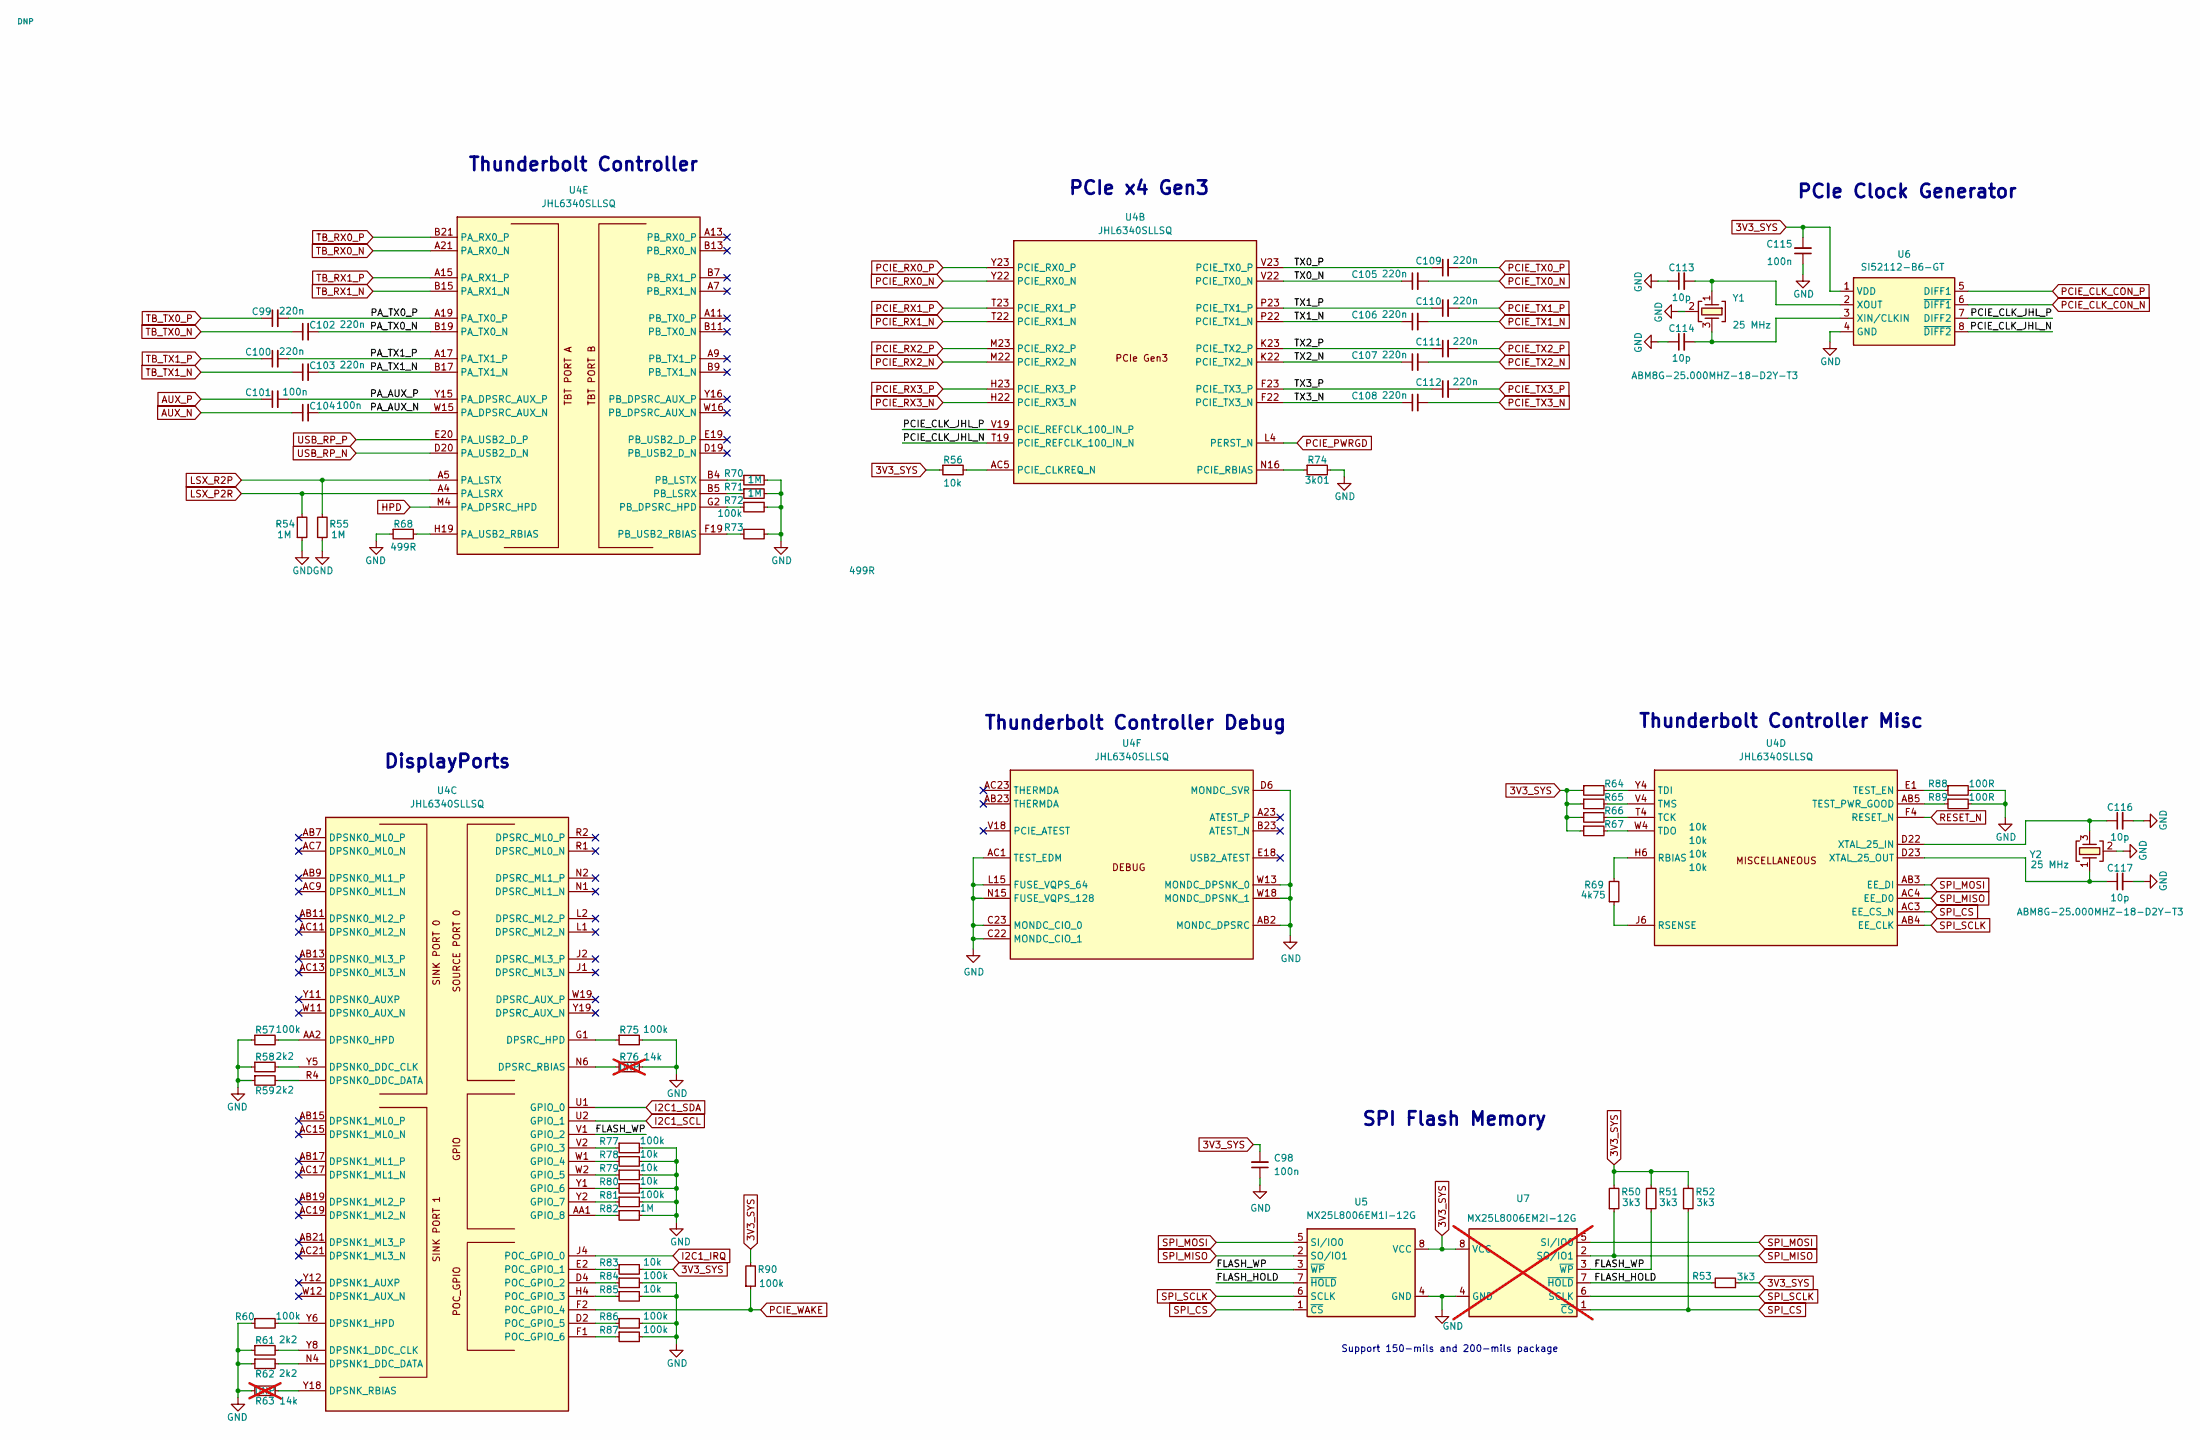
[picture p5: schematic tb.kicad_sch]

Parts:
C98, C101, C104, C115: C_100n_0402; C_0402_1005Metric; Voltage 50V; MPN GRM155R61H104KE14D
C99, C100, C102, C103, C105, C106, C107, C108, C109, C110, C111, C112: C_220n_0402; C_0402_1005Metric; MPN CC0402KRX5R6BB224
C113, C114, C116, C117: C_10p_0402; C_0402_1005Metric; Voltage 50V; MPN GCM1555C1H100GA16D
R50, R51, R52, R53: R_3k3_0402; R_0402_1005Metric; Tolerance 1%; MPN CR0402-FX-3301GLF
R54, R55, R70, R71, R82: R_1M_0402; R_0402_1005Metric; Tolerance 1%; MPN CR0402-FX-1004GLF
R56, R64, R65, R66, R67, R78, R79, R80, R83, R85: R_10k_0402; R_0402_1005Metric; Tolerance 1%; MPN CR0402-FX-1002GLF
R57, R60, R72, R75, R77, R81, R84, R86, R87, R90: R_100k_0402; R_0402_1005Metric; Tolerance 1%; MPN CR0402-FX-1003GLF
R58, R59, R61, R62: R_2k2_0402; R_0402_1005Metric; Tolerance 1%; MPN CR0402-FX-2201GLF
R63, R76: R_14k_0402; R_0402_1005Metric; Tolerance 1%; MPN CR0402-FX-1402GLF; not fitted
R68, R73: R_499R_0402; R_0402_1005Metric; Tolerance 1%; MPN CR0402-FX-4990GLF
R69: R_4k75_0.5%_0402; R_0402_1005Metric; Tolerance 0.5%; MPN ERJ-H2RD4751X
R74: R_3k01_0402; R_0402_1005Metric; Tolerance 1%; MPN CR0402-FX-3011GLF
R88, R89: R_100R_0402; R_0402_1005Metric; Tolerance 1%; MPN CR0402-FX-1000GLF
U4: JHL6340SLLSQ; MPN JHL6340SLLSQ
U5: MX25L8006EM1I-12G; SOIC-8_3.9x4.9x1.75mm_P1.27mm; MPN MX25L8006EM1I-12G
U6: SI52112-B6-GT; TSSOP-8_3x4.4mm_P0.65mm; MPN SI52112-B6-GT
U7: MX25L8006EM2I-12G; SOIC-8_5.3x5.3x2mm_P1.27mm; MPN MX25L8006EM2I-12G; not fitted
Y1, Y2: Resonator_25MHz_ABM8G; Resonator_SMD_Abracon_ABM8G_3.2x2.5mm; MPN ABM8G-25.000MHZ-18-D2Y-T3

Connections:
3V3_SYS: C98.2, C115.2, R50.2, R51.2, R52.2, R53.1, R56.1, R64.1, R65.1, R66.1, R67.1, R83.2, R90.2, U5.8 (VCC), U6.1 (VDD), U7.8 (VCC)
AUX_N: C104.1
AUX_P: C101.1
FLASH_HOLD: R53.2, U5.7 (~HOLD), U7.7 (~HOLD)
FLASH_WP: R51.1, U4.V1 (GPIO_2), U5.3 (~WP), U7.3 (~WP)
GND: C98.1, C113.1, C114.1, C115.1, C116.2, C117.2, R54.1, R55.1, R57.1, R58.1, R59.1, R60.1, R61.1, R62.1, R63.1, R68.1, R70.2, R71.2, R72.2, R73.2, R74.2, R75.2, R76.2, R77.2, R78.2, R79.2, R80.2, R81.2, R82.2, R84.2, R85.2, R86.2, R87.2, R88.2, R89.2, U4.AB2 (MONDC_DPSRC), U4.AC1 (TEST_EDM), U4.C22 (MONDC_CIO_1), U4.C23 (MONDC_CIO_0), U4.D6 (MONDC_SVR), U4.L15 (FUSE_VQPS_64), U4.N15 (FUSE_VQPS_128), U4.W13 (MONDC_DPSNK_0), U4.W18 (MONDC_DPSNK_1), U5.4 (GND), U6.4 (GND), U7.4 (GND), Y1.2 (SH), Y1.4 (SH), Y2.2 (SH), Y2.4 (SH)
HPD: U4.M4 (PA_DPSRC_HPD)
I2C1_IRQ: U4.J4 (POC_GPIO_0)
I2C1_SCL: U4.U2 (GPIO_1)
I2C1_SDA: U4.U1 (GPIO_0)
LSX_P2R: R54.2, U4.A4 (PA_LSRX)
LSX_R2P: R55.2, U4.A5 (PA_LSTX)
unnamed: C113.2, U6.2 (XOUT), Y1.1
unnamed: C114.2, U6.3 (XIN/CLKIN), Y1.3
unnamed: C116.1, U4.D22 (XTAL_25_IN), Y2.3
unnamed: C117.1, U4.D23 (XTAL_25_OUT), Y2.1
unnamed: R56.2, U4.AC5 (PCIE_CLKREQ_N)
unnamed: R57.2, U4.AA2 (DPSNK0_HPD)
unnamed: R58.2, U4.Y5 (DPSNK0_DDC_CLK)
unnamed: R59.2, U4.R4 (DPSNK0_DDC_DATA)
unnamed: R60.2, U4.Y6 (DPSNK1_HPD)
unnamed: R61.2, U4.Y8 (DPSNK1_DDC_CLK)
unnamed: R62.2, U4.N4 (DPSNK1_DDC_DATA)
unnamed: R63.2, U4.Y18 (DPSNK_RBIAS)
unnamed: R64.2, U4.Y4 (TDI)
unnamed: R65.2, U4.V4 (TMS)
unnamed: R66.2, U4.T4 (TCK)
unnamed: R67.2, U4.W4 (TDO)
unnamed: R68.2, U4.H19 (PA_USB2_RBIAS)
unnamed: R69.1, U4.J6 (RSENSE)
unnamed: R69.2, U4.H6 (RBIAS)
unnamed: R70.1, U4.B4 (PB_LSTX)
unnamed: R71.1, U4.B5 (PB_LSRX)
unnamed: R72.1, U4.G2 (PB_DPSRC_HPD)
unnamed: R73.1, U4.F19 (PB_USB2_RBIAS)
unnamed: R74.1, U4.N16 (PCIE_RBIAS)
unnamed: R75.1, U4.G1 (DPSRC_HPD)
unnamed: R76.1, U4.N6 (DPSRC_RBIAS)
unnamed: R77.1, U4.V2 (GPIO_3)
unnamed: R78.1, U4.W1 (GPIO_4)
unnamed: R79.1, U4.W2 (GPIO_5)
unnamed: R80.1, U4.Y1 (GPIO_6)
unnamed: R81.1, U4.Y2 (GPIO_7)
unnamed: R82.1, U4.AA1 (GPIO_8)
unnamed: R83.1, U4.E2 (POC_GPIO_1)
unnamed: R84.1, U4.D4 (POC_GPIO_2)
unnamed: R85.1, U4.H4 (POC_GPIO_3)
unnamed: R86.1, U4.D2 (POC_GPIO_5)
unnamed: R87.1, U4.F1 (POC_GPIO_6)
unnamed: R88.1, U4.E1 (TEST_EN)
unnamed: R89.1, U4.AB5 (TEST_PWR_GOOD)
PA_AUX_N: C104.2, U4.W15 (PA_DPSRC_AUX_N)
PA_AUX_P: C101.2, U4.Y15 (PA_DPSRC_AUX_P)
PA_TX0_N: C102.2, U4.B19 (PA_TX0_N)
PA_TX0_P: C99.2, U4.A19 (PA_TX0_P)
PA_TX1_N: C103.2, U4.B17 (PA_TX1_N)
PA_TX1_P: C100.2, U4.A17 (PA_TX1_P)
PCIE_CLK_CON_N: U6.6 (~DIFF1)
PCIE_CLK_CON_P: U6.5 (DIFF1)
PCIE_CLK_JHL_N: U4.T19 (PCIE_REFCLK_100_IN_N), U6.8 (~DIFF2)
PCIE_CLK_JHL_P: U4.V19 (PCIE_REFCLK_100_IN_P), U6.7 (DIFF2)
PCIE_PWRGD: U4.L4 (PERST_N)
PCIE_RX0_N: U4.Y22 (PCIE_RX0_N)
PCIE_RX0_P: U4.Y23 (PCIE_RX0_P)
PCIE_RX1_N: U4.T22 (PCIE_RX1_N)
PCIE_RX1_P: U4.T23 (PCIE_RX1_P)
PCIE_RX2_N: U4.M22 (PCIE_RX2_N)
PCIE_RX2_P: U4.M23 (PCIE_RX2_P)
PCIE_RX3_N: U4.H22 (PCIE_RX3_N)
PCIE_RX3_P: U4.H23 (PCIE_RX3_P)
PCIE_TX0_N: C105.2
PCIE_TX0_P: C109.2
PCIE_TX1_N: C106.2
PCIE_TX1_P: C110.2
PCIE_TX2_N: C107.2
PCIE_TX2_P: C111.2
PCIE_TX3_N: C108.2
PCIE_TX3_P: C112.2
PCIE_WAKE: R90.1, U4.F2 (POC_GPIO_4)
RESET_N: U4.F4 (RESET_N)
SPI_CS: R52.1, U4.AC3 (EE_CS_N), U5.1 (~CS), U7.1 (~CS)
SPI_MISO: R50.1, U4.AC4 (EE_D0), U5.2 (SO/IO1), U7.2 (SO/IO1)
SPI_MOSI: U4.AB3 (EE_DI), U5.5 (SI/IO0), U7.5 (SI/IO0)
SPI_SCLK: U4.AB4 (EE_CLK), U5.6 (SCLK), U7.6 (SCLK)
TB_RX0_N: U4.A21 (PA_RX0_N)
TB_RX0_P: U4.B21 (PA_RX0_P)
TB_RX1_N: U4.B15 (PA_RX1_N)
TB_RX1_P: U4.A15 (PA_RX1_P)
TB_TX0_N: C102.1
TB_TX0_P: C99.1
TB_TX1_N: C103.1
TB_TX1_P: C100.1
TX0_N: C105.1, U4.V22 (PCIE_TX0_N)
TX0_P: C109.1, U4.V23 (PCIE_TX0_P)
TX1_N: C106.1, U4.P22 (PCIE_TX1_N)
TX1_P: C110.1, U4.P23 (PCIE_TX1_P)
TX2_N: C107.1, U4.K22 (PCIE_TX2_N)
TX2_P: C111.1, U4.K23 (PCIE_TX2_P)
TX3_N: C108.1, U4.F22 (PCIE_TX3_N)
TX3_P: C112.1, U4.F23 (PCIE_TX3_P)
USB_RP_N: U4.D20 (PA_USB2_D_N)
USB_RP_P: U4.E20 (PA_USB2_D_P)

Notes on the sheet:
DisplayPorts
Thunderbolt Controller Misc
PCIe Clock Generator
SPI Flash Memory
Thunderbolt Controller
Thunderbolt Controller Debug
Support 150-mils and 200-mils package
PCIe x4 Gen3
