KataFF/tbt-pcie-adapter/thunderbolt-pcie-adapter.kicad_sch

## KiCad design thunderbolt-pcie-adapter.kicad_sch (2025-07-04)

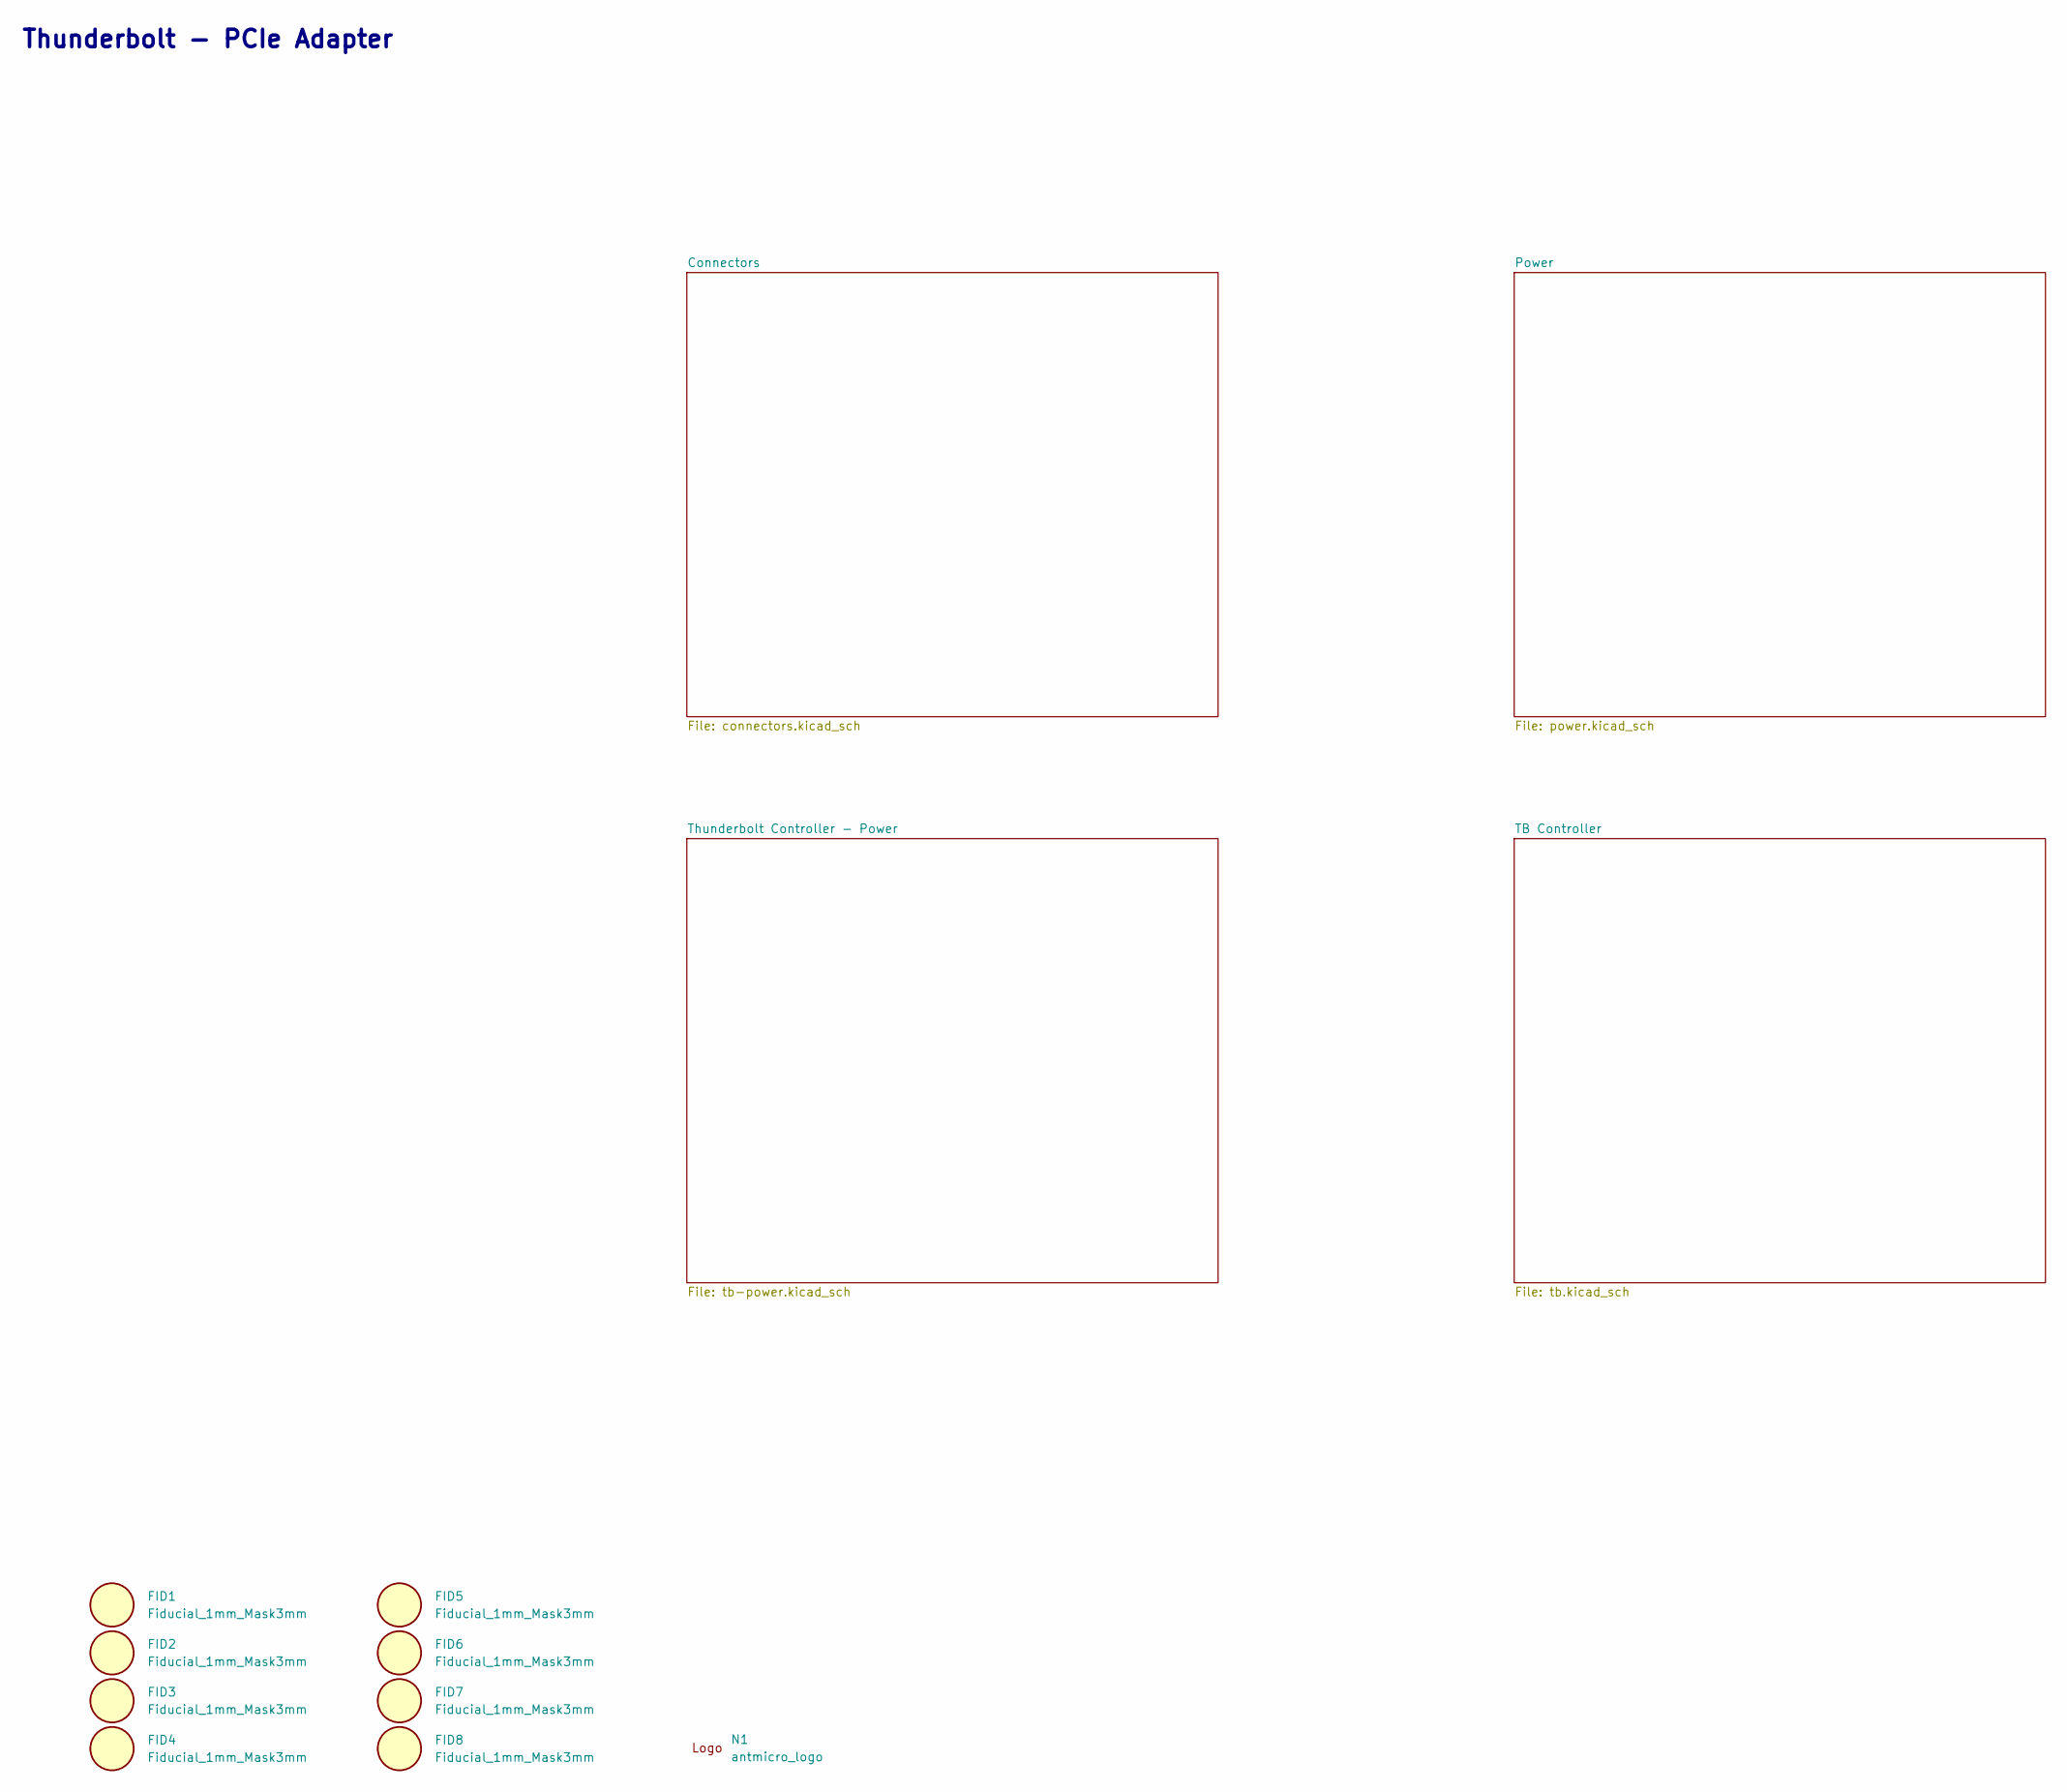
[picture p6: schematic thunderbolt-pcie-adapter.kicad_sch]

Parts:
FID1, FID2, FID3, FID4, FID5, FID6, FID7, FID8: Fiducial_1mm_Mask3mm
N1: antmicro_logo; antmicro-logo_scaled_12mm_mask

Notes on the sheet:
Thunderbolt - PCIe Adapter
